StefanKDS/CWKeyer/CWKeyer/ESPOLED.cpp

#include <Wire.h>
#include "ESPOLED.h"
#include "Defines.h"

//==========================================================//

// Small 8x8 font
static const char myFont[][8] PROGMEM = {  
{0x00,0x00,0x00,0x00,0x00,0x00,0x00,0x00},
{0x00,0x00,0x5F,0x00,0x00,0x00,0x00,0x00},
{0x00,0x00,0x07,0x00,0x07,0x00,0x00,0x00},
{0x00,0x14,0x7F,0x14,0x7F,0x14,0x00,0x00},
{0x00,0x24,0x2A,0x7F,0x2A,0x12,0x00,0x00},
{0x00,0x23,0x13,0x08,0x64,0x62,0x00,0x00},
{0x00,0x36,0x49,0x55,0x22,0x50,0x00,0x00},
{0x00,0x00,0x05,0x03,0x00,0x00,0x00,0x00},
{0x00,0x1C,0x22,0x41,0x00,0x00,0x00,0x00},
{0x00,0x41,0x22,0x1C,0x00,0x00,0x00,0x00},
{0x00,0x08,0x2A,0x1C,0x2A,0x08,0x00,0x00},
{0x00,0x08,0x08,0x3E,0x08,0x08,0x00,0x00},
{0x00,0xA0,0x60,0x00,0x00,0x00,0x00,0x00},
{0x00,0x08,0x08,0x08,0x08,0x08,0x00,0x00},
{0x00,0x60,0x60,0x00,0x00,0x00,0x00,0x00},
{0x00,0x20,0x10,0x08,0x04,0x02,0x00,0x00},
{0x00,0x3E,0x51,0x49,0x45,0x3E,0x00,0x00},
{0x00,0x00,0x42,0x7F,0x40,0x00,0x00,0x00},
{0x00,0x62,0x51,0x49,0x49,0x46,0x00,0x00},
{0x00,0x22,0x41,0x49,0x49,0x36,0x00,0x00},
{0x00,0x18,0x14,0x12,0x7F,0x10,0x00,0x00},
{0x00,0x27,0x45,0x45,0x45,0x39,0x00,0x00},
{0x00,0x3C,0x4A,0x49,0x49,0x30,0x00,0x00},
{0x00,0x01,0x71,0x09,0x05,0x03,0x00,0x00},
{0x00,0x36,0x49,0x49,0x49,0x36,0x00,0x00},
{0x00,0x06,0x49,0x49,0x29,0x1E,0x00,0x00},
{0x00,0x00,0x36,0x36,0x00,0x00,0x00,0x00},
{0x00,0x00,0xAC,0x6C,0x00,0x00,0x00,0x00},
{0x00,0x08,0x14,0x22,0x41,0x00,0x00,0x00},
{0x00,0x14,0x14,0x14,0x14,0x14,0x00,0x00},
{0x00,0x41,0x22,0x14,0x08,0x00,0x00,0x00},
{0x00,0x02,0x01,0x51,0x09,0x06,0x00,0x00},
{0x00,0x32,0x49,0x79,0x41,0x3E,0x00,0x00},
{0x00,0x7E,0x09,0x09,0x09,0x7E,0x00,0x00},
{0x00,0x7F,0x49,0x49,0x49,0x36,0x00,0x00},
{0x00,0x3E,0x41,0x41,0x41,0x22,0x00,0x00},
{0x00,0x7F,0x41,0x41,0x22,0x1C,0x00,0x00},
{0x00,0x7F,0x49,0x49,0x49,0x41,0x00,0x00},
{0x00,0x7F,0x09,0x09,0x09,0x01,0x00,0x00},
{0x00,0x3E,0x41,0x41,0x51,0x72,0x00,0x00},
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
};


//==========================================================//
// Resets display depending on the actual mode.
void OLED::reset_display(void)
{
  displayOff();
  clear_display();
  displayOn();
}

//==========================================================//
// Turns display on.
void OLED::displayOn(void)
{
  sendcommand(0xaf);        //display on
}

//==========================================================//
// Turns display off.
void OLED::displayOff(void)
{
  sendcommand(0xae);    //display off
}

//==========================================================//
// Clears the display by sendind 0 to all the screen map.
void OLED::clear_display(void)
{
  unsigned char i,k;
  for(k=0;k<8;k++)
  { 
    setXY(k,0);    
    {
      for(i=0;i<(128 + 2 * _offset);i++)     //locate all COL
      {
        SendChar(0);         //clear all COL
        //delay(10);
      }
    }
  }
}

//==========================================================//
// Actually this sends a byte, not a char to draw in the display. 
// Display's chars uses 8 byte font the small ones and 96 bytes
// for the big number font.
void OLED::SendChar(unsigned char data) 
{
  //if (interrupt && !doing_menu) return;   // Stop printing only if interrupt is call but not in button functions
  
  Wire.beginTransmission(_address); // begin transmitting
  Wire.write(0x40);//data mode
  Wire.write(data);
  Wire.endTransmission();    // stop transmitting
}

//==========================================================//
// Prints a display char (not just a byte) in coordinates X Y,
// being multiples of 8. This means we have 16 COLS (0-15) 
// and 8 ROWS (0-7).
void OLED::sendCharXY(unsigned char data, int X, int Y)
{
  setXY(X, Y);
  Wire.beginTransmission(_address); // begin transmitting
  Wire.write(0x40);//data mode
  
  for(int i=0;i<8;i++)          
    Wire.write(pgm_read_byte(myFont[data-0x20]+i));
    
  Wire.endTransmission();    // stop transmitting
}

//==========================================================//
// Used to send commands to the display.
void OLED::sendcommand(unsigned char com)
{
  Wire.beginTransmission(_address);     //begin transmitting
  Wire.write(0x80);                          //command mode
  Wire.write(com);
  Wire.endTransmission();                    // stop transmitting
}

//==========================================================//
// Set the cursor position in a 16 COL * 8 ROW map.
void OLED::setXY(unsigned char row,unsigned char col)
{
  sendcommand(0xb0+row);                //set page address
  sendcommand(_offset+(8*col&0x0f));       //set low col address
  sendcommand(0x10+((8*col>>4)&0x0f));  //set high col address
}


//==========================================================//
// Prints a string regardless the cursor position.
void OLED::sendStr(unsigned char *string)
{
  unsigned char i=0;
  while(*string)
  {
    for(i=0;i<8;i++)
    {
      SendChar(pgm_read_byte(myFont[*string-0x20]+i));
    }
    *string++;
  }
}

//==========================================================//
// Prints a string in coordinates X Y, being multiples of 8.
// This means we have 16 COLS (0-15) and 8 ROWS (0-7).
void OLED::sendStrXY(const char *string, int X, int Y)
{
    setXY(X, Y);
    unsigned char i = 0;

    while (*string)
    {
        uint8_t fontIndex = 0;

        // Prüfe auf UTF-8 Umlaute (ä, ö, ü)
        if ((unsigned char)*string == 0xC3)  // UTF-8 Prefix für Umlaute
        {
            string++; // zum zweiten Byte der UTF-8 Sequenz

            if ((unsigned char)*string == 0xA4) // ä
                fontIndex = sizeof(myFont) / 8 - 3;
            else if ((unsigned char)*string == 0xB6) // ö
                fontIndex = sizeof(myFont) / 8 - 2;
            else if ((unsigned char)*string == 0xBC) // ü
                fontIndex = sizeof(myFont) / 8 - 1;
            else
                fontIndex = 0; // unbekannt → Leerzeichen
        }
        else if ((unsigned char)*string >= 0x20 && (unsigned char)*string <= 0x7F)
        {
            // Normale ASCII-Zeichen
            fontIndex = *string - 0x20;
        }
        else
        {
            fontIndex = 0; // Platzhalter
        }

        // Zeichen aus Font ausgeben
        for (i = 0; i < 8; i++)
        {
            SendChar(pgm_read_byte(myFont[fontIndex] + i));
        }

        string++; // zum nächsten Zeichen
    }
}


//==========================================================//
// Inits oled and draws logo at startup
void OLED::init_OLED(void)
{
    sendcommand(0xae);            //display off
    sendcommand(0xa6);            //Set Normal Display (default)
    // Adafruit Init sequence for 128x64 OLED module
    sendcommand(0xAE);            //DISPLAYOFF
    sendcommand(0xD5);            //SETDISPLAYCLOCKDIV
    sendcommand(0x80);            // the suggested ratio 0x80
    sendcommand(0xA8);            //SSD1306_SETMULTIPLEX
    sendcommand(0x3F);
    sendcommand(0xD3);            //SETDISPLAYOFFSET
    sendcommand(0x0);             //no offset
    sendcommand(0x40 | 0x0);      //SETSTARTLINE
    sendcommand(0x8D);            //CHARGEPUMP
    sendcommand(0x14);
    sendcommand(0x20);             //MEMORYMODE
    sendcommand(0x00);             //0x0 act like ks0108
    
    //sendcommand(0xA0 | 0x1);      //SEGREMAP   //Rotate screen 180 deg
    sendcommand(0xA0);
    
    //sendcommand(0xC8);            //COMSCANDEC  Rotate screen 180 Deg
    sendcommand(0xC0);
    
    sendcommand(0xDA);            //0xDA
    sendcommand(0x12);           //COMSCANDEC
    sendcommand(0x81);           //SETCONTRAS
    sendcommand(0xCF);           //
    sendcommand(0xd9);            //SETPRECHARGE 
    sendcommand(0xF1); 
    sendcommand(0xDB);            //SETVCOMDETECT                
    sendcommand(0x40);
    sendcommand(0xA4);            //DISPLAYALLON_RESUME        
    sendcommand(0xA6);          //NORMALDISPLAY             

    clear_display();
    sendcommand(0x2e);            // stop scroll

  sendcommand(0x20);            //Set Memory Addressing Mode
  sendcommand(0x00);            //Set Memory Addressing Mode ab Horizontal addressing mode 
}


//==========================================================//


OLED::OLED(uint8_t sda, uint8_t scl, uint8_t address, uint8_t offset) {
  _sda = sda;
  _scl = scl;
  _address = address;
  _offset = offset;
}

void OLED::begin(void) {
  // set up i2c
  Wire.begin(_sda, _scl);
  init_OLED();
  reset_display();
}

void OLED::on(void) {
  displayOn();
}

void OLED::off(void) {
  displayOff();
}

void OLED::clear(void) {
  clear_display();
}

void OLED::print(const char *s, uint8_t r, uint8_t c) {
  sendStrXY(s, r, c);
}
